shreaypatel/446MHz-Tape-Measure-Yagi/Media/image3.jpg

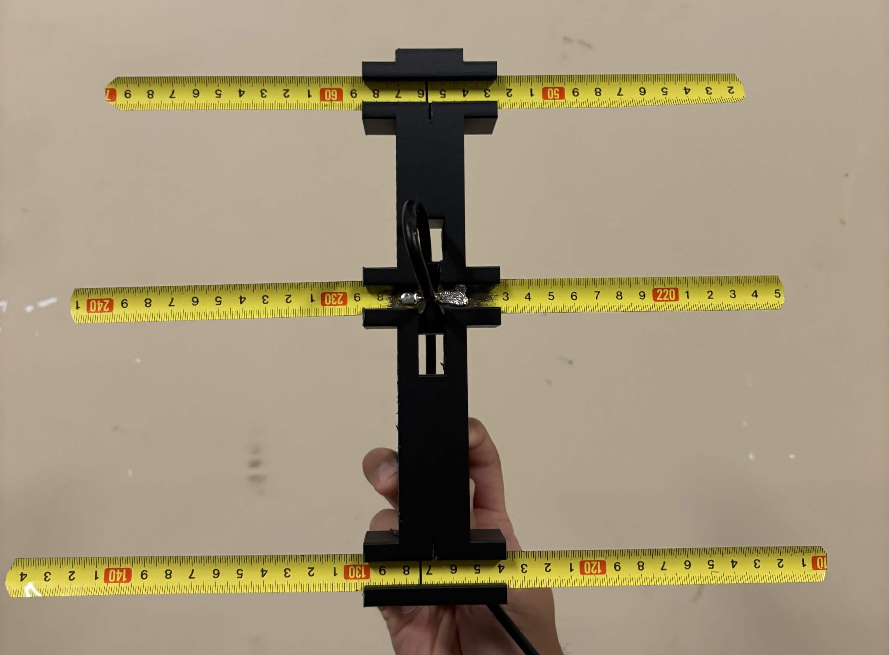
Media/image3.jpg
