shreaypatel/446MHz-Tape-Measure-Yagi/Media/image4.jpg

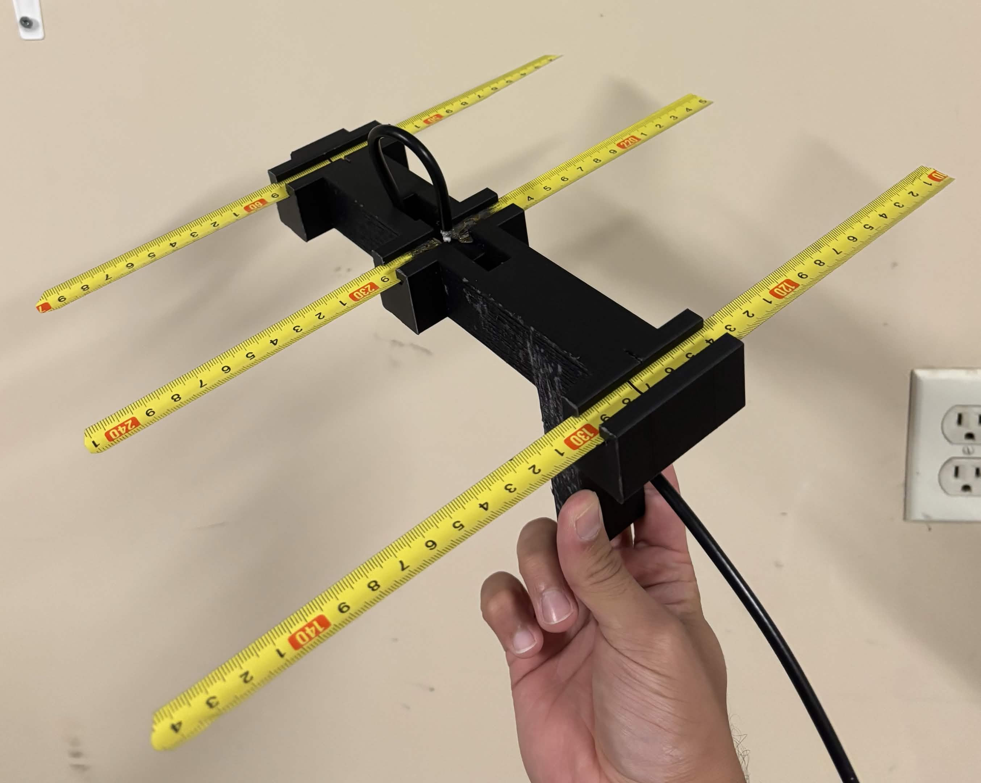
Media/image4.jpg
